michaelthatsit/mod/buttons/default/README.md

Q: Where's default size? What should I print?! \
A: You can start with D850 H1.2 — it's a pretty neutral option.

Q: What does D850 or H3.6 mean? \
A: D = curve diameter, H = distance from the ball center.

example
