michaelthatsit/mod/57-68mm ball (50-60mm with spacers)/insert/README.md

# Insert

A little part just for aesthetics, if you aren't planning to use ≥57mm balls. \
Supposed to be carefully glued in like this:



# Demo (with 52.4mm ball)
