michaelthatsit/mod/57-68mm ball (50-60mm with spacers)/btu-spacer/README.md

## BTU Spacer

Install 3 spacers to make the mod work with 50-60mm balls instead of 57-68mm. \
Example:
