michaelthatsit/mod/44-45mm ball (+ short version)/standard/images/45mm-top.png

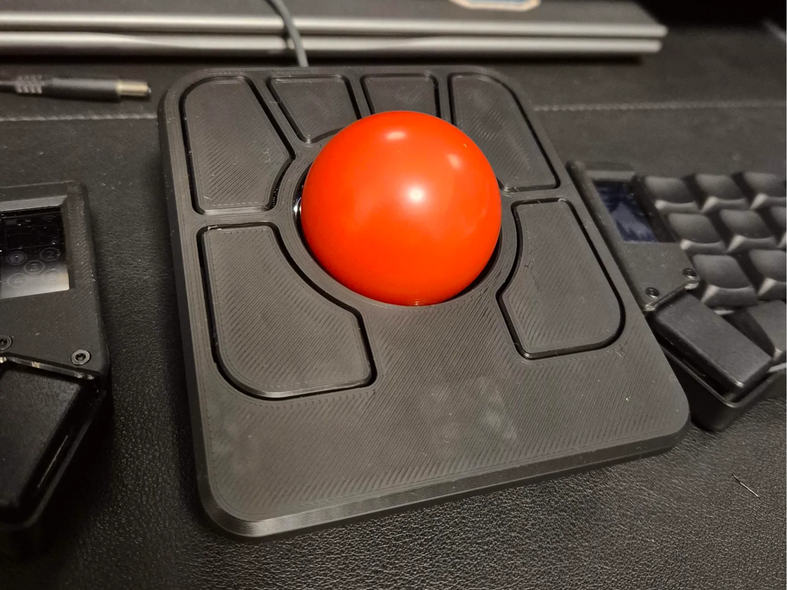
44-45mm ball (+ short version)/standard/images/45mm-top.png
