michaelthatsit/mod/50-52.5mm ball/rev 2/raised-buttons/example.png

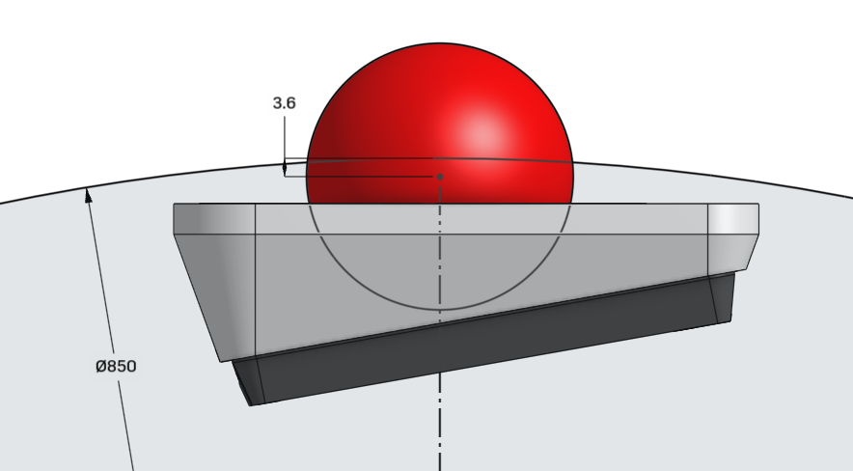
50-52.5mm ball/rev 2/raised-buttons/example.png
