michaelthatsit/mod/adapters/Static-3mm-no-glue.step

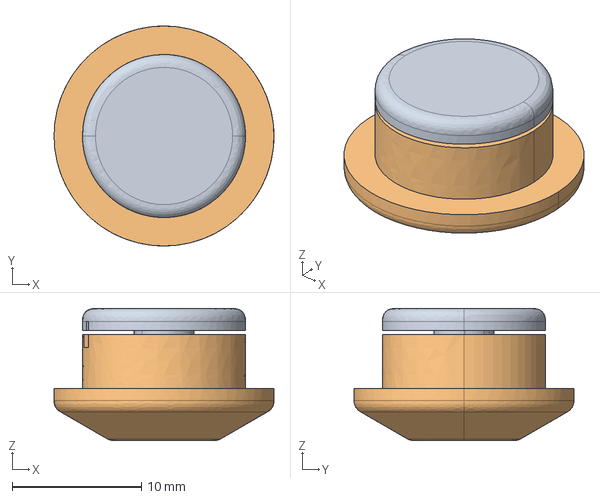
[picture p42: CAD file, 2025-04-21]
adapters/Static-3mm-no-glue.step
17.0 x 17.0 x 10.2 mm
