michaelthatsit/mod/buttons/default/D625/D625 H2.4.step

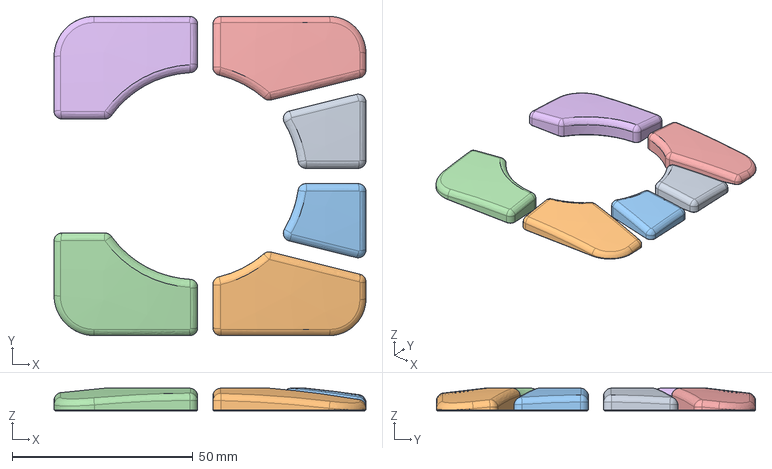
[picture p43: CAD file, 2025-02-22]
buttons/default/D625/D625 H2.4.step
86.4 x 88.4 x 6.28 mm
