michaelthatsit/mod/buttons/default/D750/D750 H1.2.step

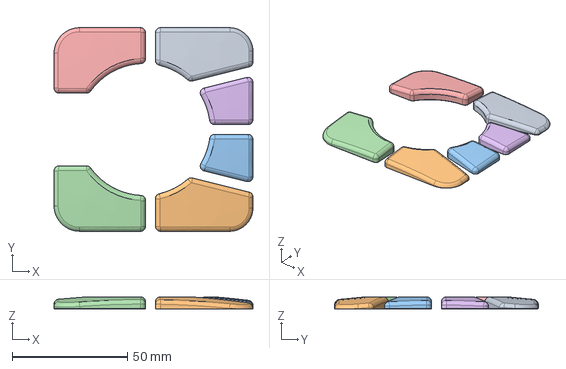
[picture p44: CAD file, 2025-02-22]
buttons/default/D750/D750 H1.2.step
86.4 x 88.4 x 5.33 mm
