michaelthatsit/mod/buttons/default/D850/D850 H2.4.step

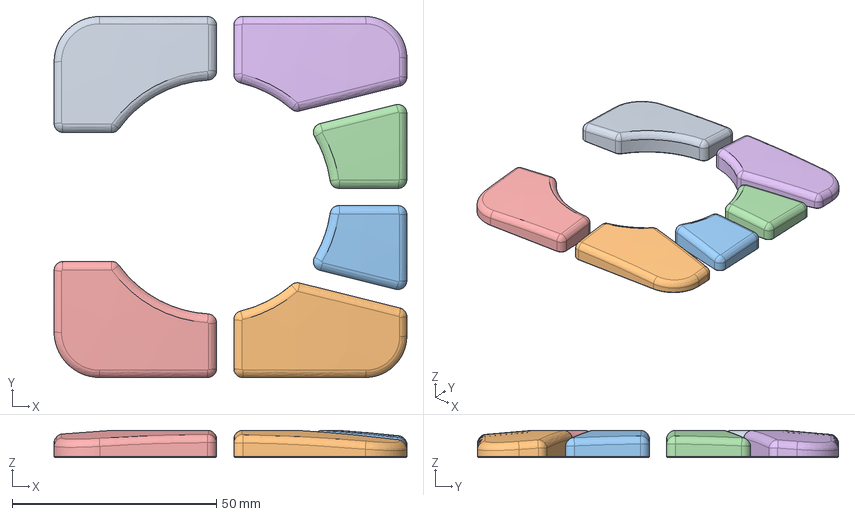
[picture p45: CAD file, 2025-02-22]
buttons/default/D850/D850 H2.4.step
86.4 x 88.4 x 6.68 mm
