michaelthatsit/mod/buttons/default/D950/D950 H3.6.step

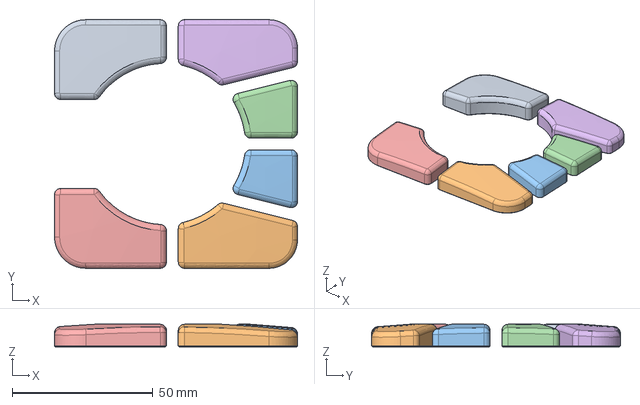
[picture p46: CAD file, 2025-02-22]
buttons/default/D950/D950 H3.6.step
86.4 x 88.4 x 8.00 mm
