michaelthatsit/mod/buttons/flat-5mm/flat-buttons-5mm.step

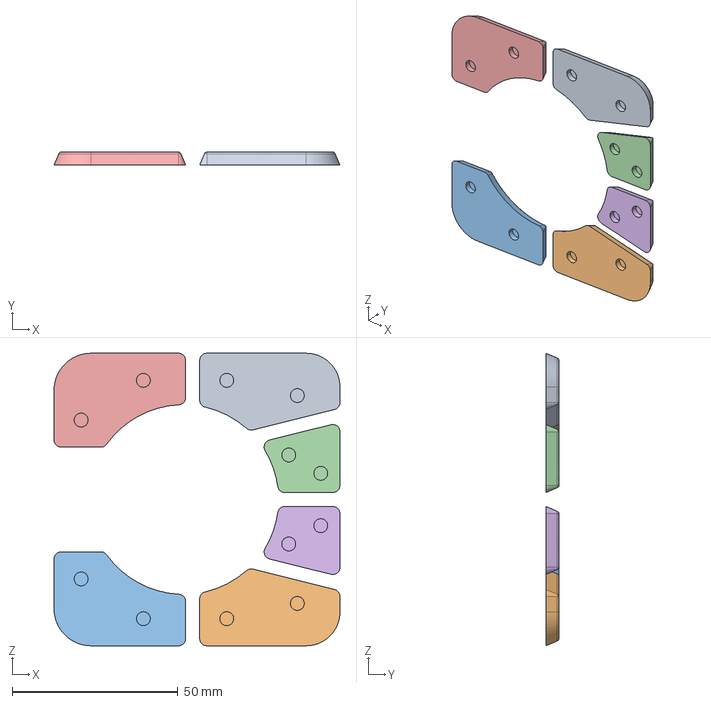
[picture p47: CAD file, 2025-02-22]
buttons/flat-5mm/flat-buttons-5mm.step
86.4 x 4.00 x 88.4 mm
