michaelthatsit/mod/spacers/Spacer 0.4mm.step

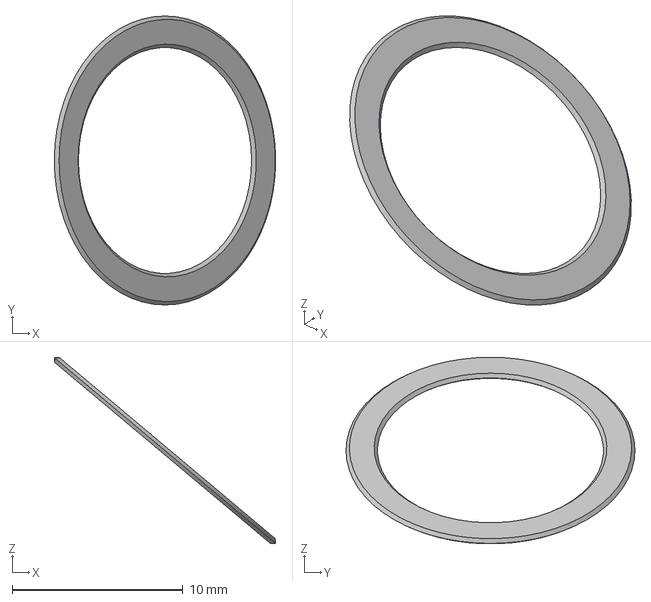
[picture p48: CAD file, 2025-02-23]
spacers/Spacer 0.4mm.step
13.0 x 16.9 x 10.9 mm
