michaelthatsit/mod/44-45mm ball (+ short version)/short/top-short-battery.step

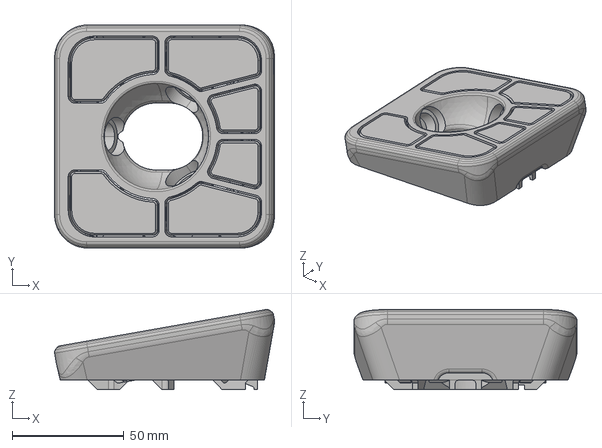
[picture p49: CAD file, 2025-08-10]
44-45mm ball (+ short version)/short/top-short-battery.step
98.6 x 100.0 x 35.9 mm
