michaelthatsit/mod/50-55mm ball (short, thin bezel)/STEP/BTU top for MJF.step

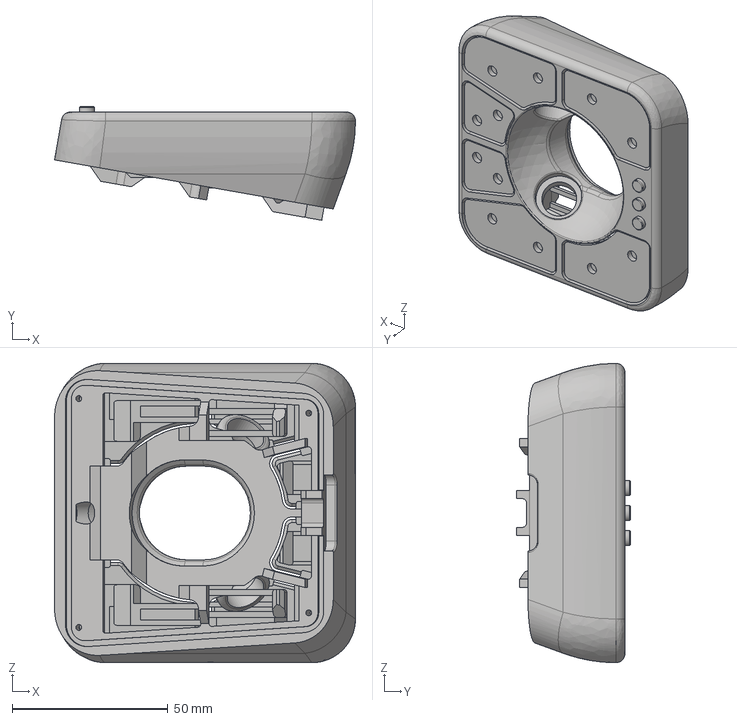
[picture p50: CAD file, 2025-04-10]
50-55mm ball (short, thin bezel)/STEP/BTU top for MJF.step
96.5 x 36.4 x 96.0 mm
