michaelthatsit/mod/50-55mm ball/top-for-non-standard-Veichu15-BTUs.step

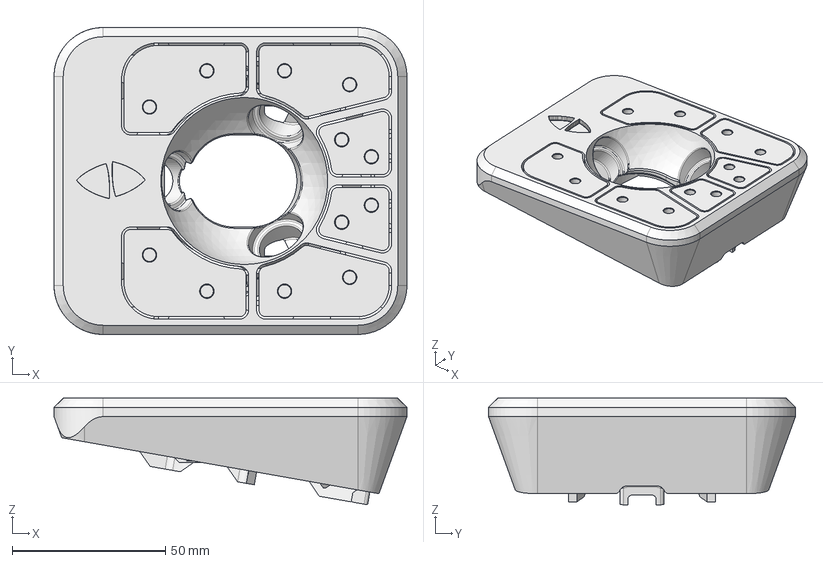
[picture p51: CAD file, 2025-03-15]
50-55mm ball/top-for-non-standard-Veichu15-BTUs.step
115.0 x 100.0 x 34.7 mm
