michaelthatsit/mod/57-68mm ball (50-60mm with spacers)/Top.step

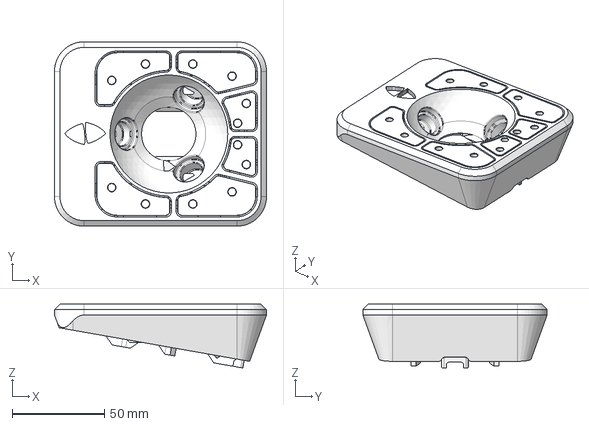
[picture p52: CAD file, 2025-02-17]
57-68mm ball (50-60mm with spacers)/Top.step
115.0 x 100.0 x 34.7 mm
