michaelthatsit/mod/buttons/default/D625/D625 H3.6.step

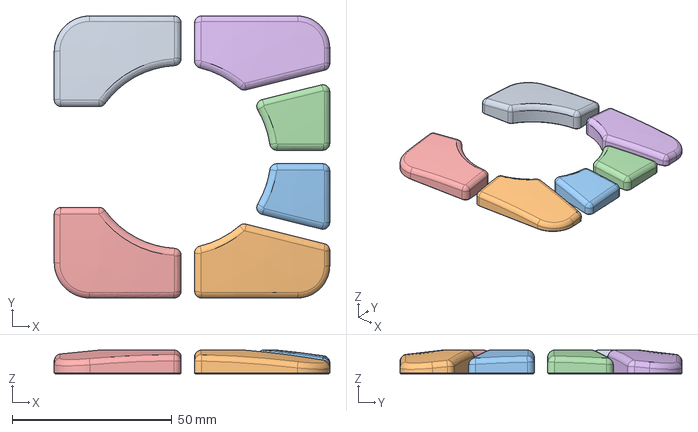
[picture p53: CAD file, 2025-02-22]
buttons/default/D625/D625 H3.6.step
86.4 x 88.4 x 7.48 mm
