michaelthatsit/mod/buttons/default/D750/D750 H2.4.step

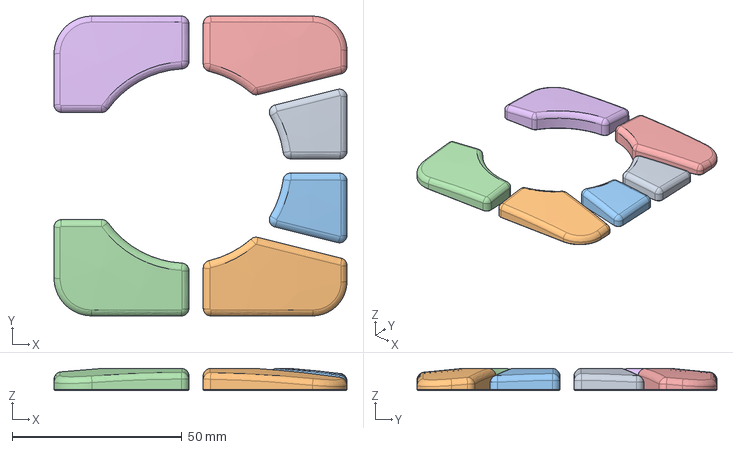
[picture p54: CAD file, 2025-02-22]
buttons/default/D750/D750 H2.4.step
86.4 x 88.4 x 6.53 mm
