michaelthatsit/mod/buttons/default/D850/D850 H1.2.step

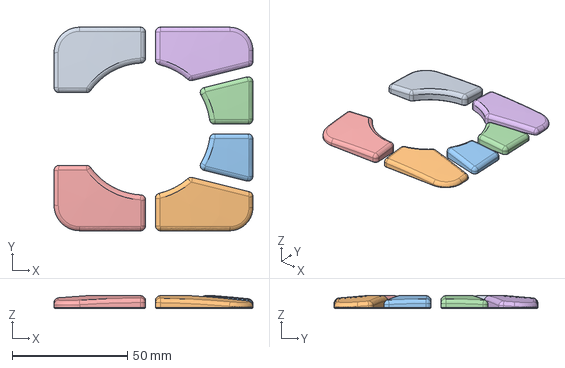
[picture p55: CAD file, 2025-02-22]
buttons/default/D850/D850 H1.2.step
86.4 x 88.4 x 5.48 mm
