michaelthatsit/mod/buttons/default/D950/D950 H0.step

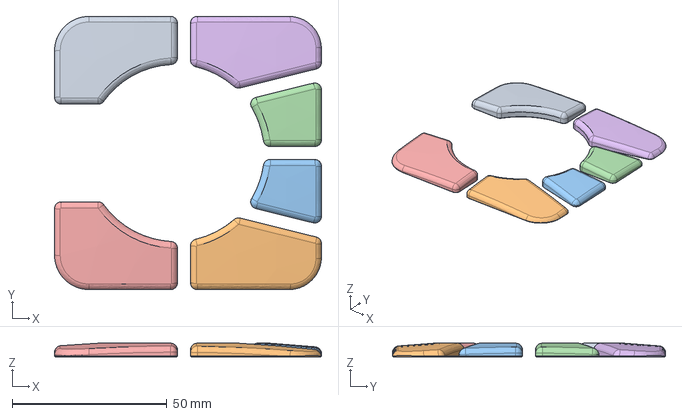
[picture p56: CAD file, 2025-02-22]
buttons/default/D950/D950 H0.step
86.4 x 88.4 x 4.40 mm
