michaelthatsit/mod/spacers/Spacer 1.2mm.step

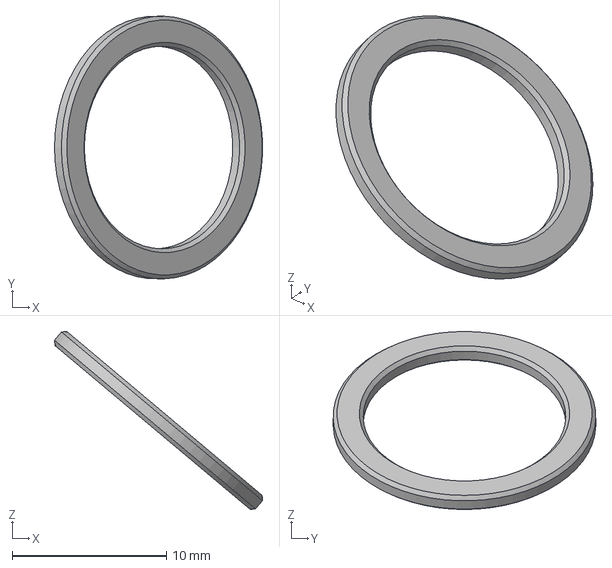
[picture p57: CAD file, 2025-02-23]
spacers/Spacer 1.2mm.step
13.5 x 17.0 x 11.6 mm
