michaelthatsit/mod/44-45mm ball (+ short version)/short/bottom-short-303048-battery.step

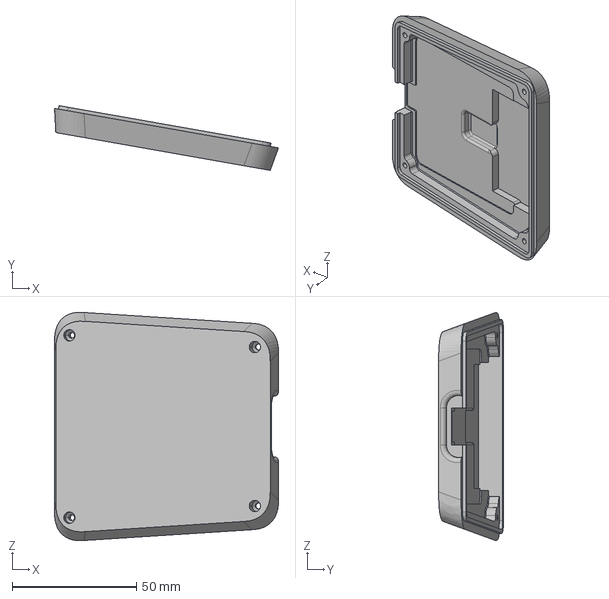
[picture p58: CAD file, 2025-02-24]
44-45mm ball (+ short version)/short/bottom-short-303048-battery.step
90.2 x 26.1 x 91.9 mm
