michaelthatsit/mod/50-52.5mm ball/rev 2/raised-buttons/D650 Concave (experimental)/H1.2/Button 2.step

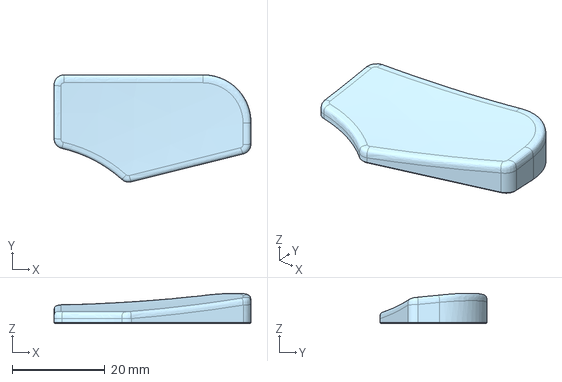
[picture p59: CAD file, 2025-02-11]
50-52.5mm ball/rev 2/raised-buttons/D650 Concave (experimental)/H1.2/Button 2.step
42.4 x 23.1 x 6.56 mm
