michaelthatsit/mod/50-52.5mm ball/rev 2/raised-buttons/D700/H2.4/Adept 50-52mm rev2 - Button 4.step

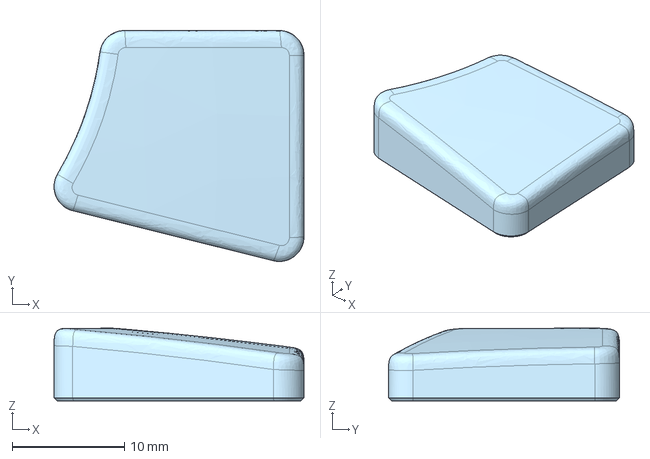
[picture p60: CAD file, 2025-02-11]
50-52.5mm ball/rev 2/raised-buttons/D700/H2.4/Adept 50-52mm rev2 - Button 4.step
22.3 x 20.6 x 6.46 mm
