michaelthatsit/mod/50-55mm ball (short version)/logo-insert-short.step

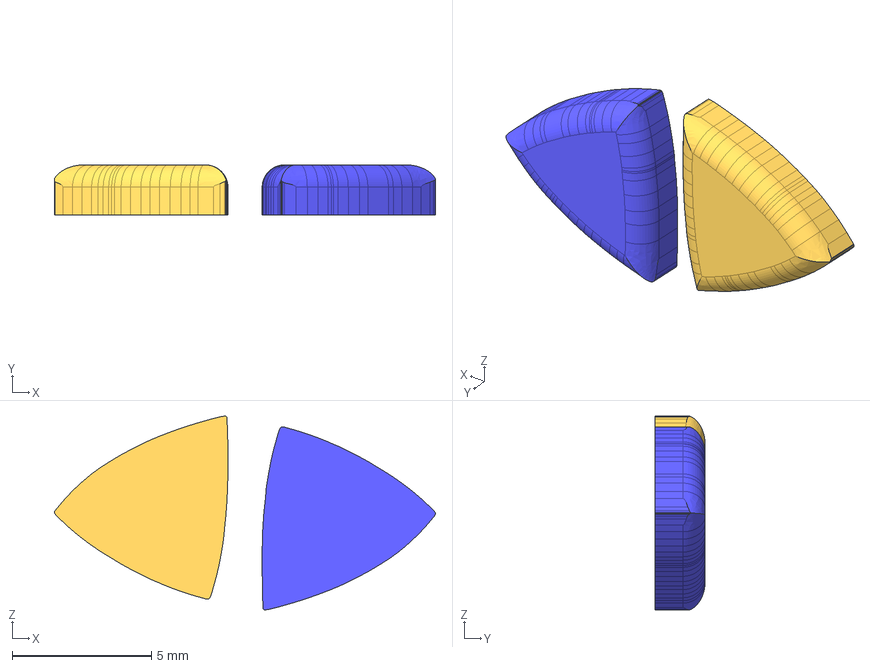
[picture p61: CAD file, 2025-02-21]
50-55mm ball (short version)/logo-insert-short.step
13.7 x 1.80 x 6.95 mm
