michaelthatsit/mod/50-55mm ball (short, thin bezel)/STEP/BTU top for FDM cham.step

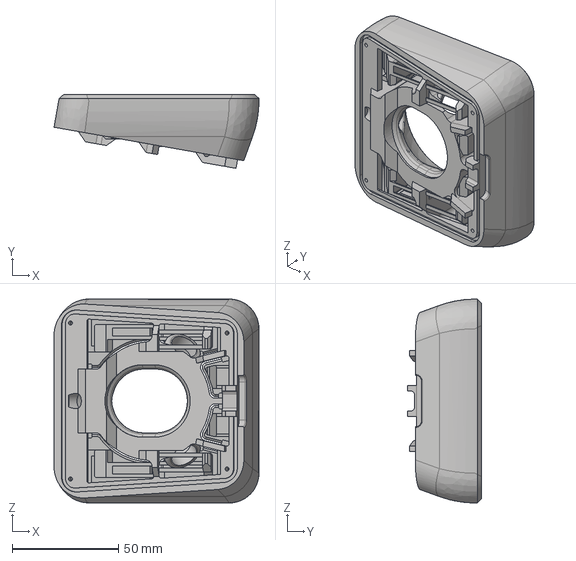
[picture p62: CAD file, 2025-04-10]
50-55mm ball (short, thin bezel)/STEP/BTU top for FDM cham.step
96.5 x 34.7 x 96.0 mm
