michaelthatsit/mod/50-55mm ball/Everything.step

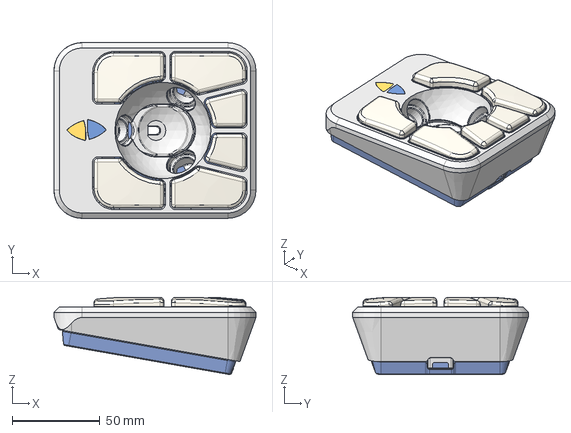
[picture p63: CAD file, 2025-02-23]
50-55mm ball/Everything.step
115.0 x 100.0 x 44.0 mm
