michaelthatsit/mod/57-68mm ball (50-60mm with spacers)/Sensor Cover.step

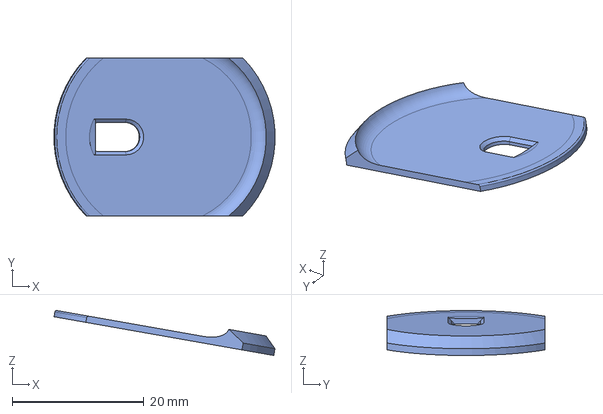
[picture p64: CAD file, 2025-02-17]
57-68mm ball (50-60mm with spacers)/Sensor Cover.step
33.5 x 23.9 x 6.83 mm
