michaelthatsit/mod/buttons/default/D750/D750 H3.6.step

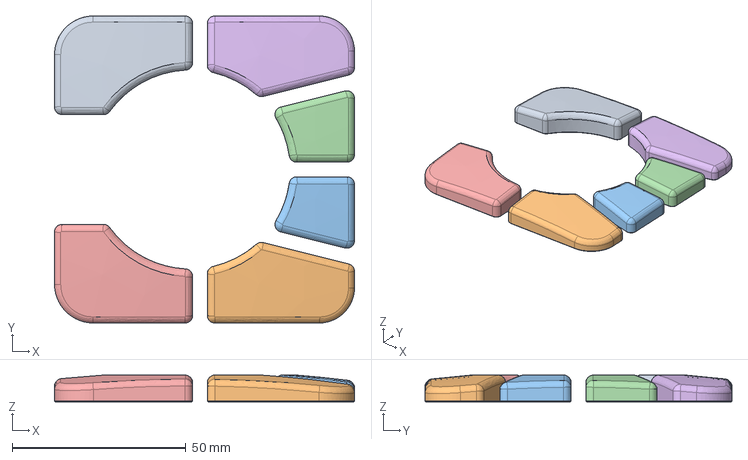
[picture p65: CAD file, 2025-02-22]
buttons/default/D750/D750 H3.6.step
86.4 x 88.4 x 7.73 mm
