michaelthatsit/mod/buttons/default/D850/D850 H3.6.step

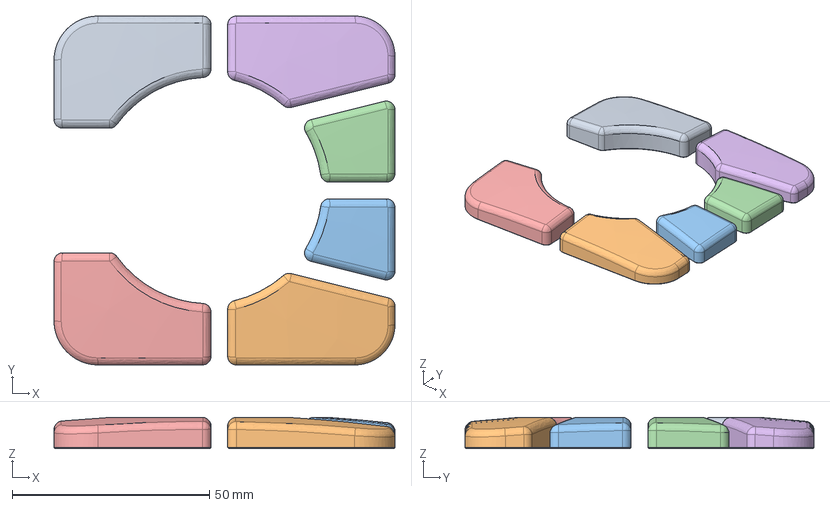
[picture p66: CAD file, 2025-02-22]
buttons/default/D850/D850 H3.6.step
86.4 x 88.4 x 7.88 mm
