michaelthatsit/mod/buttons/default/D950/D950 H2.4.step

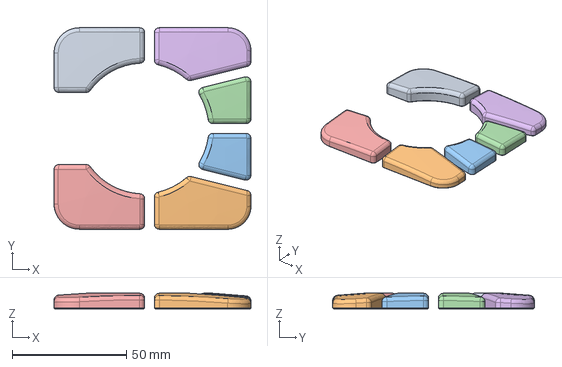
[picture p67: CAD file, 2025-02-22]
buttons/default/D950/D950 H2.4.step
86.4 x 88.4 x 6.80 mm
