michaelthatsit/mod/44-45mm ball (+ short version)/short/top-short-45mm.step

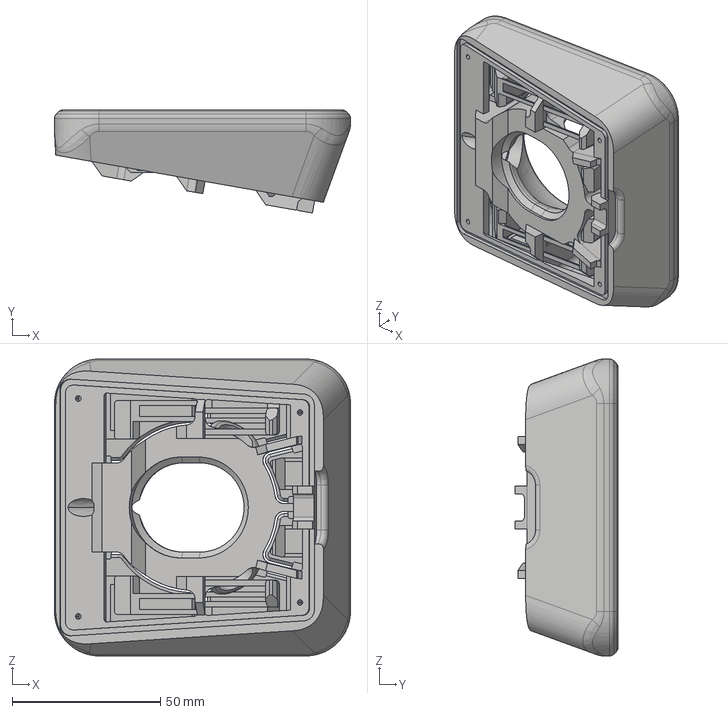
[picture p68: CAD file, 2025-02-24]
44-45mm ball (+ short version)/short/top-short-45mm.step
99.7 x 34.7 x 100.0 mm
