michaelthatsit/mod/50-52.5mm ball/rev 2/raised-buttons/D650 Concave (experimental)/H1.2/Button 1.step

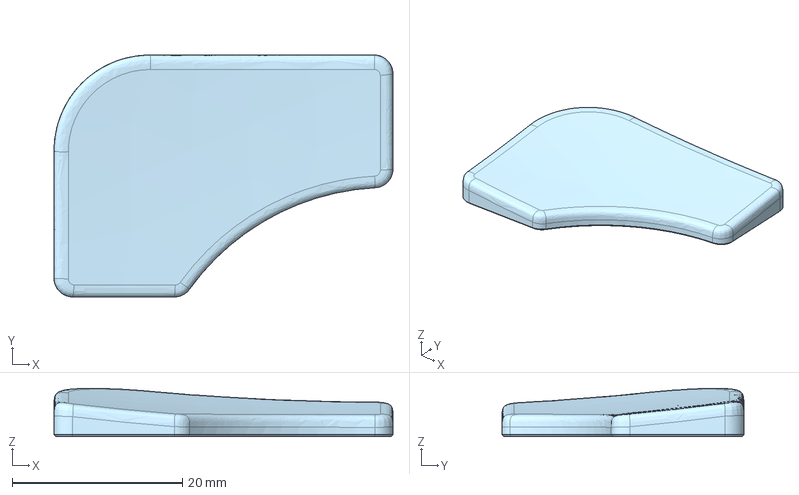
[picture p69: CAD file, 2025-02-11]
50-52.5mm ball/rev 2/raised-buttons/D650 Concave (experimental)/H1.2/Button 1.step
39.8 x 28.4 x 5.68 mm
