michaelthatsit/mod/50-52.5mm ball/rev 2/raised-buttons/D700/H2.4/Adept 50-52mm rev2 - Button 1.step

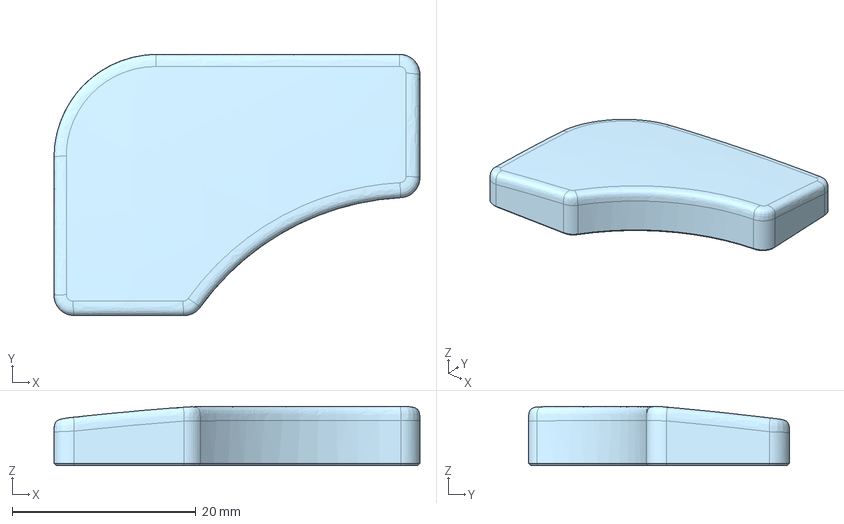
[picture p70: CAD file, 2025-02-11]
50-52.5mm ball/rev 2/raised-buttons/D700/H2.4/Adept 50-52mm rev2 - Button 1.step
39.8 x 28.4 x 6.46 mm
