michaelthatsit/mod/50-55mm ball (short, thin bezel)/STEP/BTU bottom for MJF FDM.step

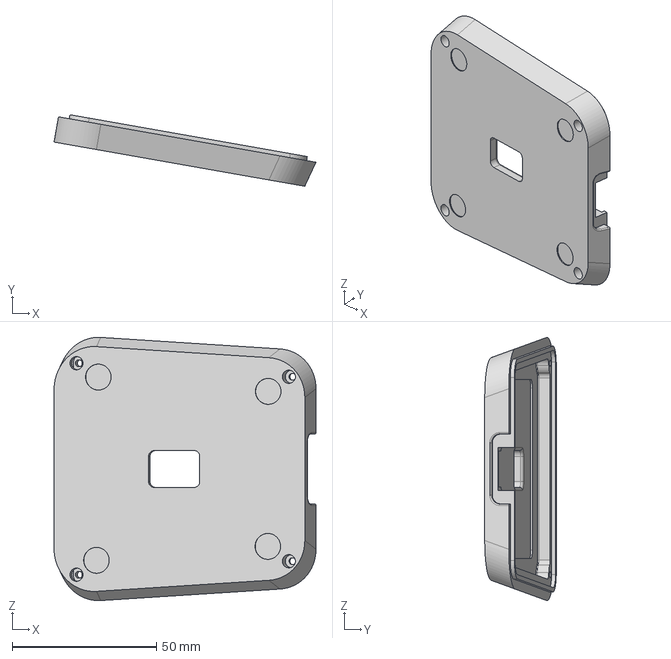
[picture p71: CAD file, 2025-04-10]
50-55mm ball (short, thin bezel)/STEP/BTU bottom for MJF FDM.step
90.9 x 24.8 x 91.3 mm
