michaelthatsit/mod/adapters/MR63-ball-bearings.step

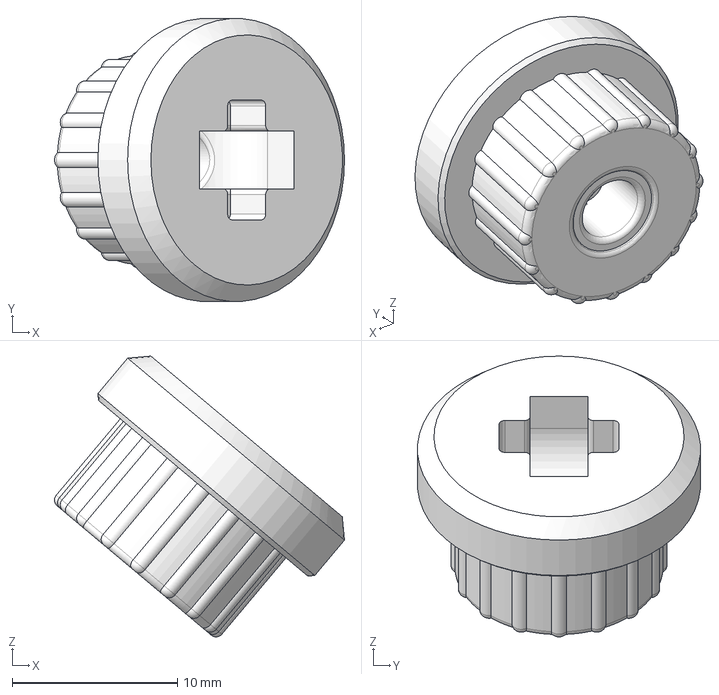
[picture p72: CAD file, 2025-04-14]
adapters/MR63-ball-bearings.step
17.6 x 17.1 x 17.0 mm
