michaelthatsit/mod/buttons/default/D950/D950 H1.2.step

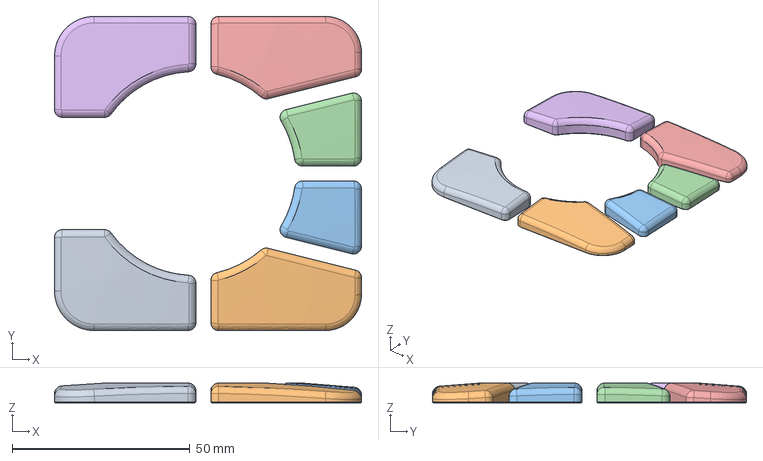
[picture p73: CAD file, 2025-02-22]
buttons/default/D950/D950 H1.2.step
86.4 x 88.4 x 5.60 mm
