michaelthatsit/mod/adapters/Static-3to3.5mm.step

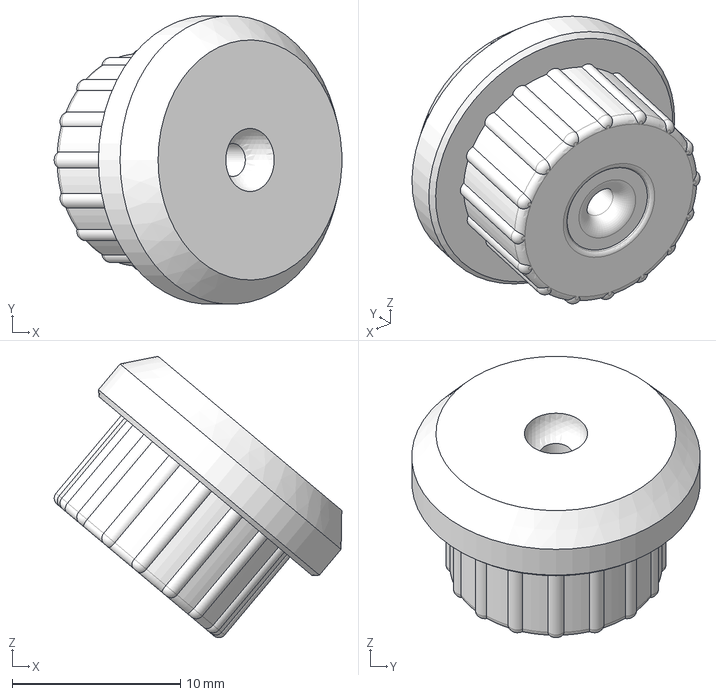
[picture p74: CAD file, 2025-03-17]
adapters/Static-3to3.5mm.step
17.1 x 17.1 x 16.7 mm
