michaelthatsit/mod/adapters/Veichu7.5.step

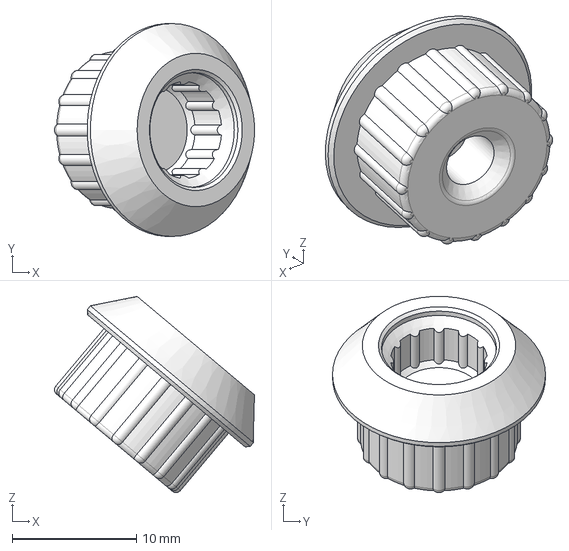
[picture p75: CAD file, 2025-02-24]
adapters/Veichu7.5.step
16.1 x 17.1 x 15.8 mm
