michaelthatsit/mod/adapters/Veichu-to-Rexroth Adapter.stl

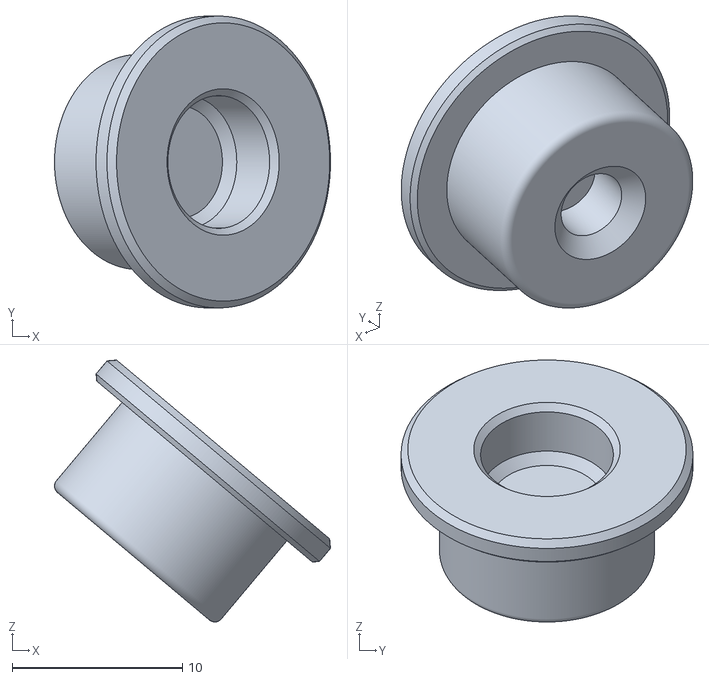
[picture p76: CAD file, 2025-02-21]
adapters/Veichu-to-Rexroth Adapter.stl
16.2 x 17.2 x 15.4
